HabonRoof/Dual-channel-waveform-generator/Image/969314.jpg

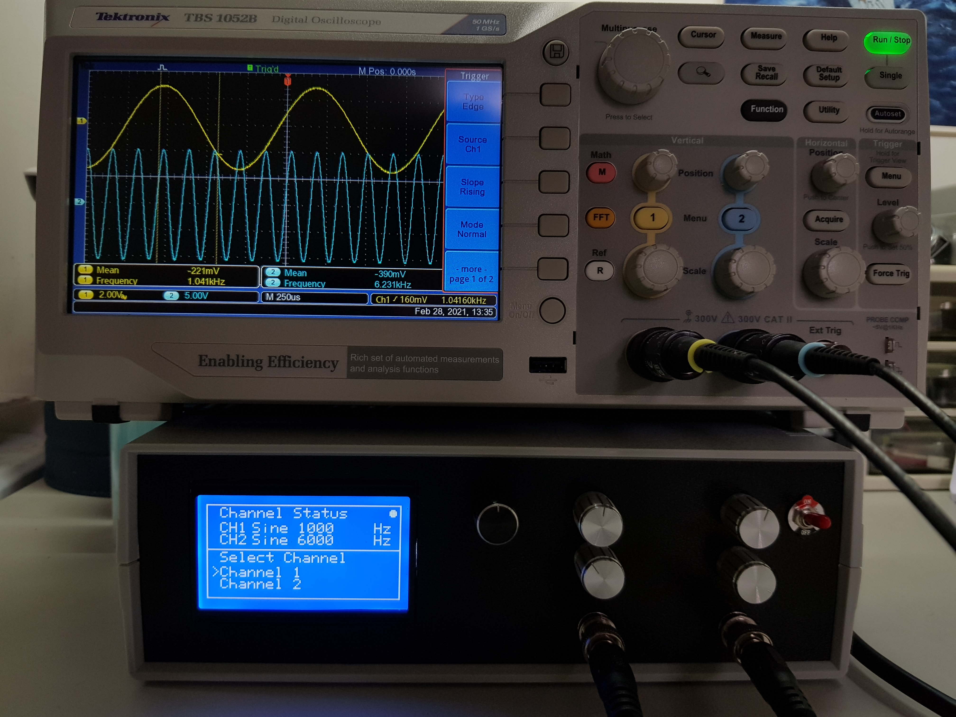
Image/969314.jpg
